chirag-parmar/walter/app/Walter/src/resources/bluetooth.png

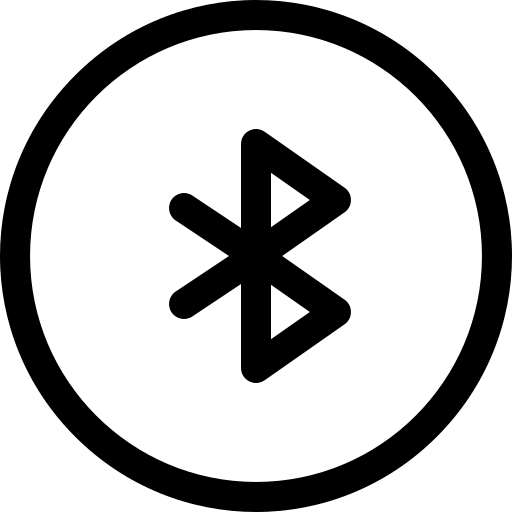
app/Walter/src/resources/bluetooth.png
